yhan0117/gamera_solar/testing/bbr/sensor mount/Sensor mount level 2 v7.step

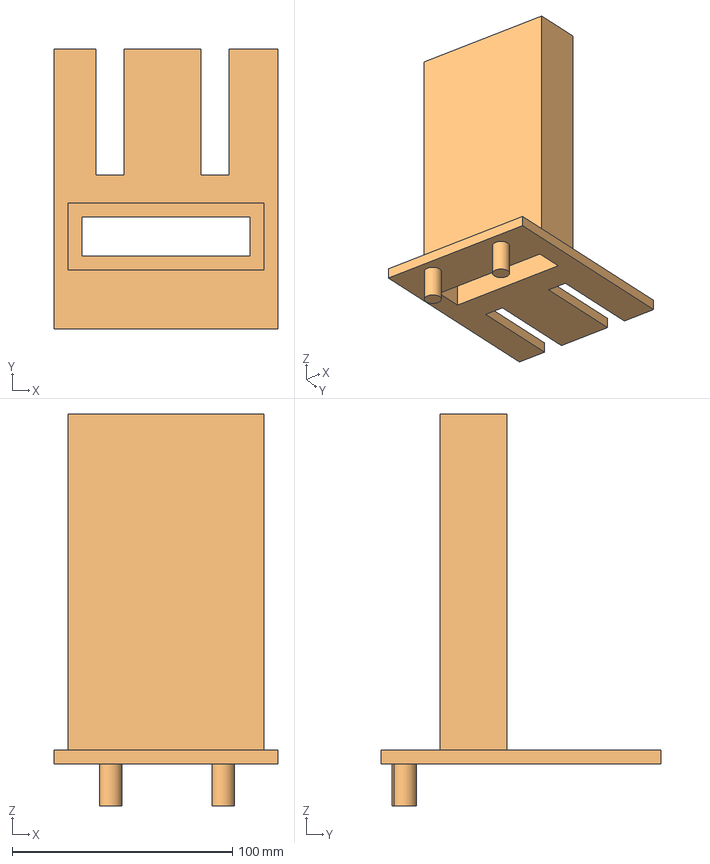
[picture p13: CAD file, 2023-09-21]
testing/bbr/sensor mount/Sensor mount level 2 v7.step
101.6 x 127.0 x 177.8 mm
