yhan0117/gamera_solar/hardware/cad/airframe/arm.SLDPRT

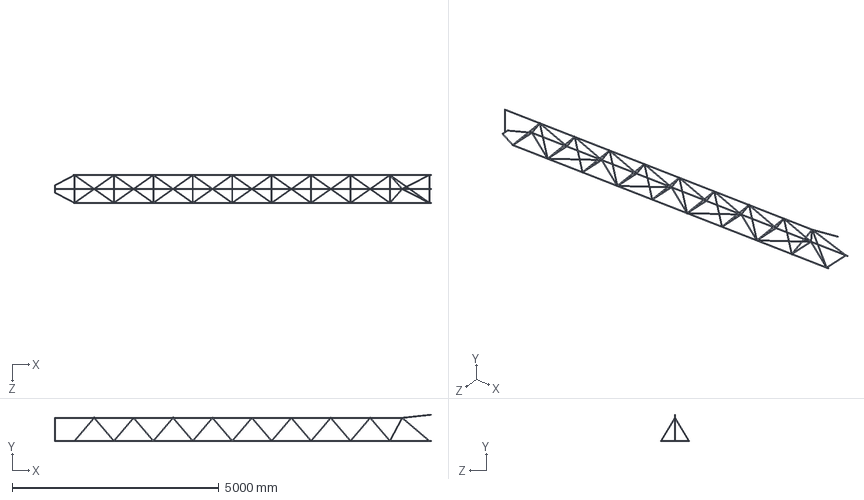
[picture p14: CAD file, 2023-09-18]
hardware/cad/airframe/arm.SLDPRT
9120.2 x 664.4 x 714.2 mm
