yhan0117/gamera_solar/hardware/cad/blades/blade foam/dxf/LESection_2_CCW_Left.dxf

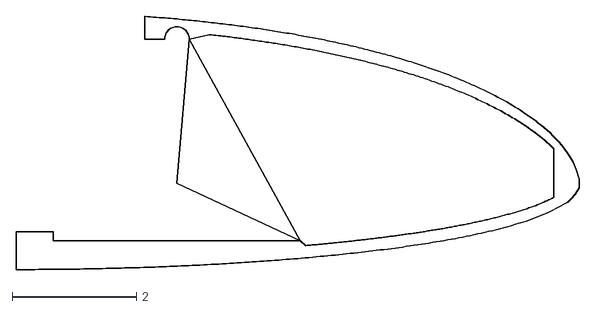
[picture p15: CAD file, 2023-09-21]
hardware/cad/blades/blade foam/dxf/LESection_2_CCW_Left.dxf
9.05 x 4.07
