yhan0117/gamera_solar/hardware/cad/blades/spar core/BladeSparCore.SLDPRT

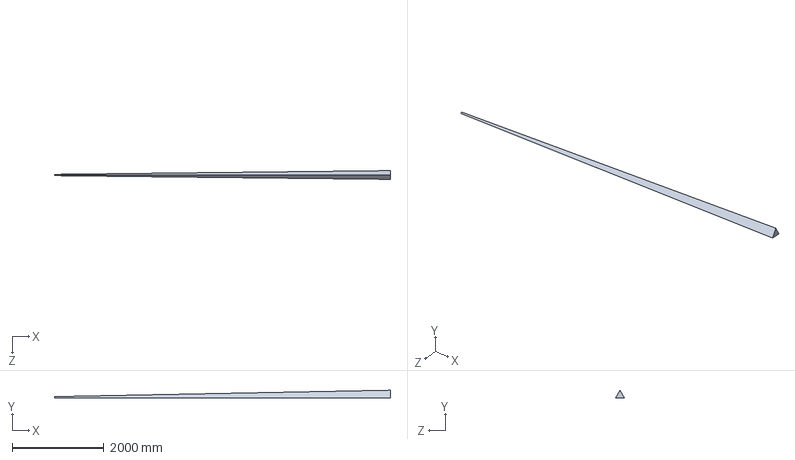
[picture p16: CAD file, 2023-09-21]
hardware/cad/blades/spar core/BladeSparCore.SLDPRT
7315.0 x 165.3 x 190.9 mm
