yhan0117/gamera_solar/hardware/cad/blades/spar core/Core1 (Root)/BladeSparCore1.SLDPRT

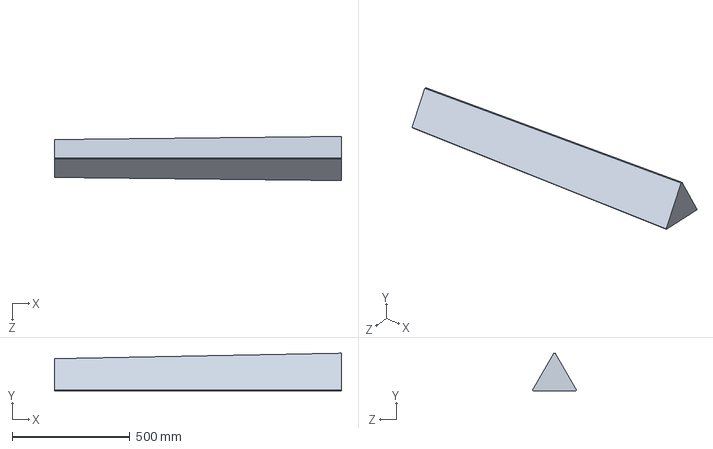
[picture p17: CAD file, 2023-09-21]
hardware/cad/blades/spar core/Core1 (Root)/BladeSparCore1.SLDPRT
1219.0 x 159.8 x 187.7 mm
