yhan0117/gamera_solar/hardware/cad/blades/spar core/Core2/BladeSparCore2.SLDPRT

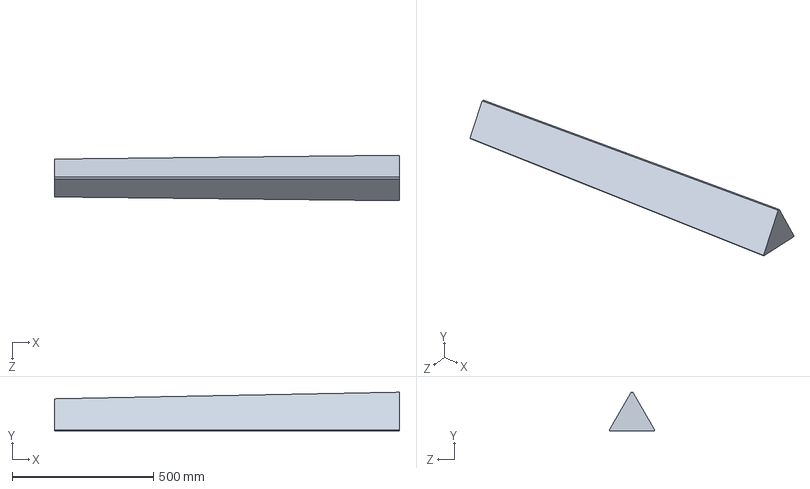
[picture p18: CAD file, 2023-09-21]
hardware/cad/blades/spar core/Core2/BladeSparCore2.SLDPRT
1219.2 x 136.5 x 160.8 mm
