yhan0117/gamera_solar/hardware/cad/blades/spar core/Core4/BladeSparCore4.SLDPRT

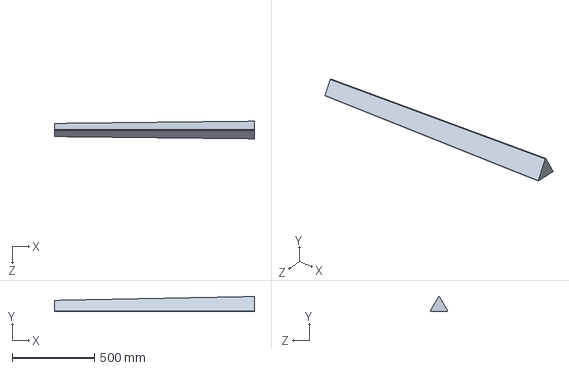
[picture p19: CAD file, 2023-09-21]
hardware/cad/blades/spar core/Core4/BladeSparCore4.SLDPRT
1219.2 x 91.1 x 107.5 mm
