yhan0117/gamera_solar/hardware/cad/blades/spar core/Core6 (Tip)/BladeSparCore6_RightFacepointsplus.DXF

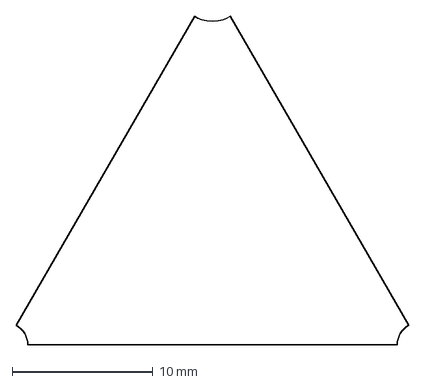
[picture p20: CAD file, 2023-09-21]
hardware/cad/blades/spar core/Core6 (Tip)/BladeSparCore6_RightFacepointsplus.DXF
27.9 x 23.3 mm
