yhan0117/gamera_solar/hardware/cad/rotor/hub/Hub_Pin_A.SLDPRT

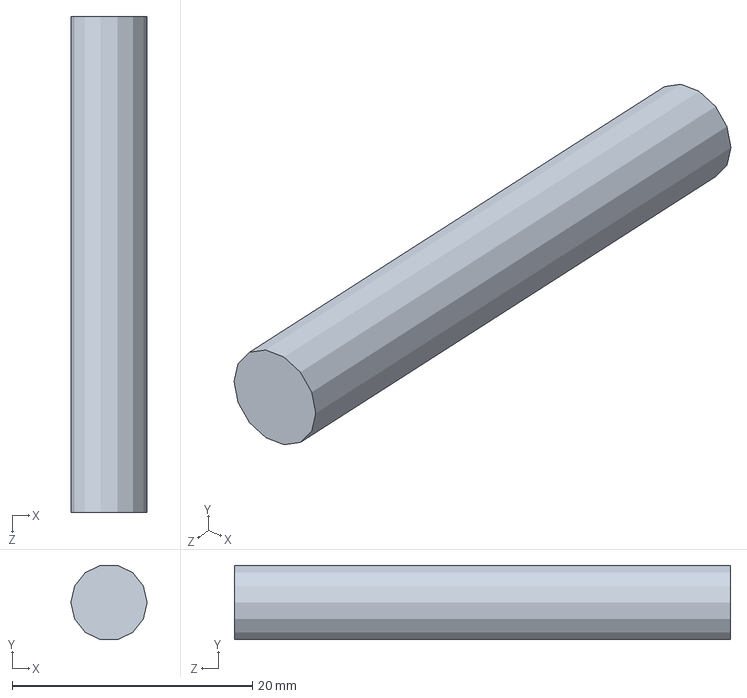
[picture p21: CAD file, 2023-09-21]
hardware/cad/rotor/hub/Hub_Pin_A.SLDPRT
6.35 x 6.19 x 41.3 mm
