yhan0117/gamera_solar/hardware/cad/rotor/landing gear/LG mold B.SLDPRT

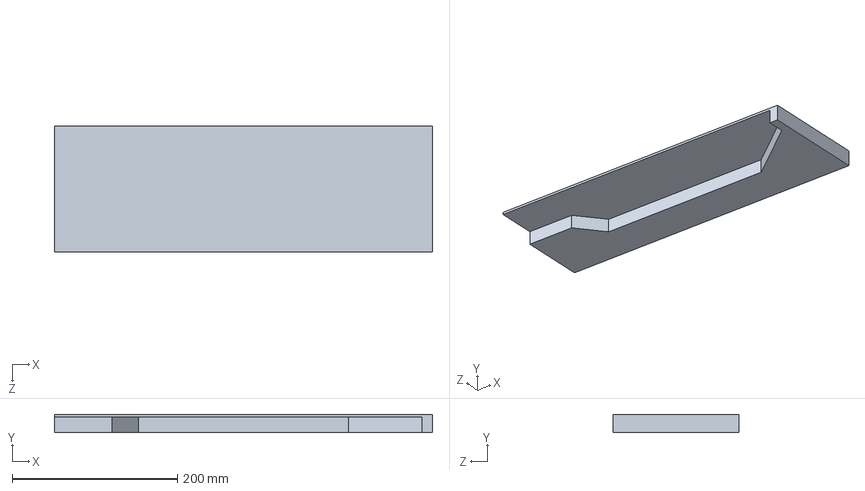
[picture p22: CAD file, 2023-09-21]
hardware/cad/rotor/landing gear/LG mold B.SLDPRT
457.2 x 22.2 x 152.4 mm
