yhan0117/gamera_solar/hardware/cad/rotor/shafts/output_shaft.SLDPRT

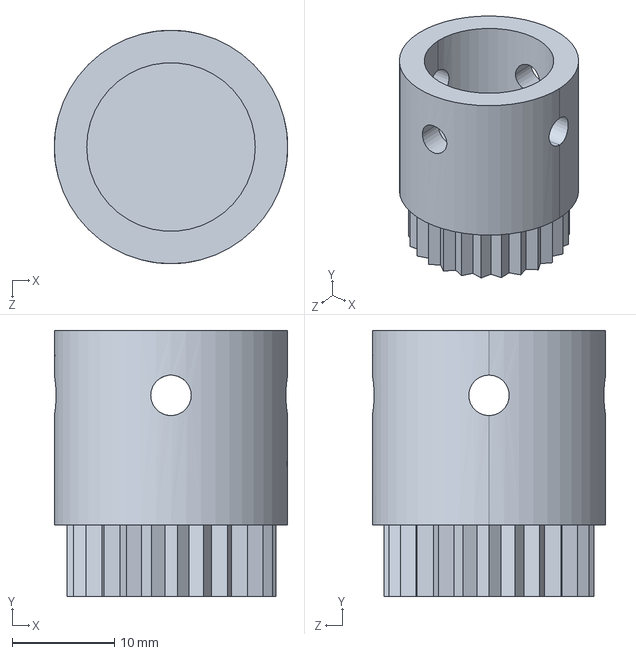
[picture p23: CAD file, 2023-09-21]
hardware/cad/rotor/shafts/output_shaft.SLDPRT
22.9 x 26.1 x 22.9 mm
