yhan0117/gamera_solar/testing/bbr/sensor mount/Sensor Mount base v9.step

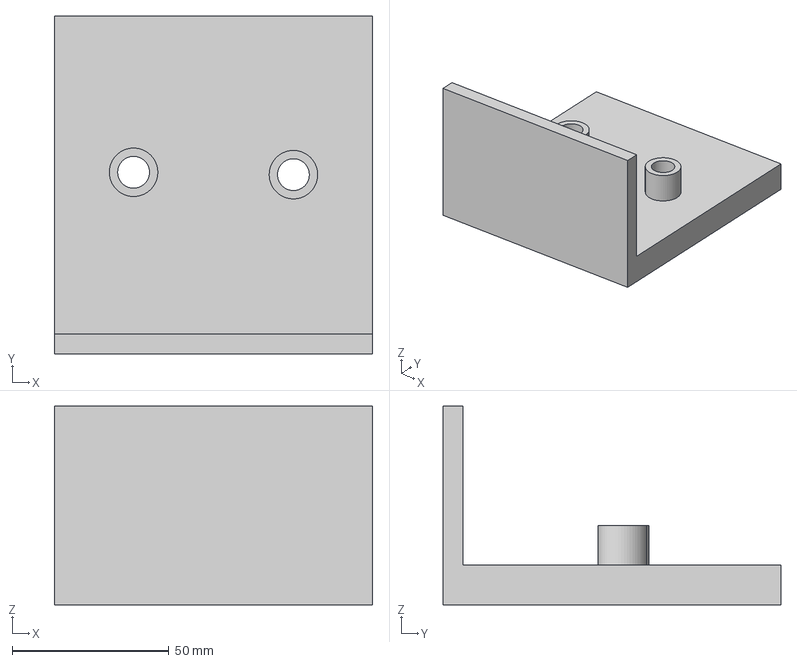
[picture p24: CAD file, 2023-09-21]
testing/bbr/sensor mount/Sensor Mount base v9.step
101.6 x 107.9 x 63.5 mm
