yhan0117/gamera_solar/hardware/cad/airframe/center.SLDPRT

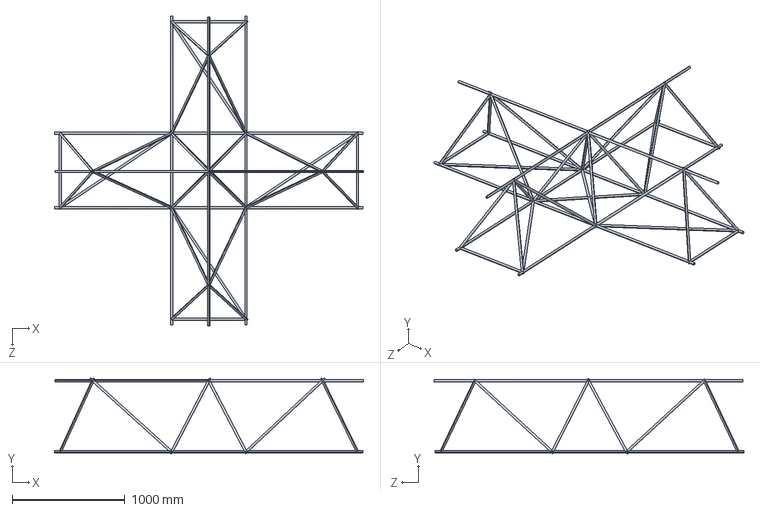
[picture p25: CAD file, 2023-09-18]
hardware/cad/airframe/center.SLDPRT
2745.7 x 673.2 x 2752.9 mm
