yhan0117/gamera_solar/hardware/cad/blades/blade foam/dxf/BladeSection_5_CCW_Right.dxf

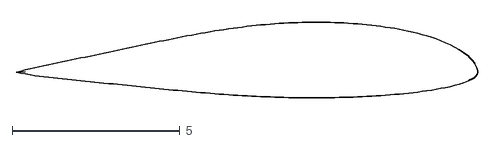
[picture p26: CAD file, 2023-09-21]
hardware/cad/blades/blade foam/dxf/BladeSection_5_CCW_Right.dxf
13.7 x 2.25
