yhan0117/gamera_solar/hardware/cad/blades/spar core/Core1 (Root)/BladeSparCore1B.DXF

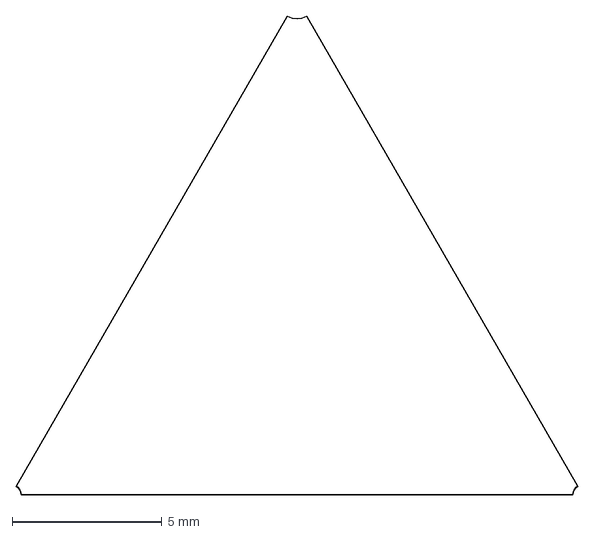
[picture p27: CAD file, 2023-09-21]
hardware/cad/blades/spar core/Core1 (Root)/BladeSparCore1B.DXF
18.8 x 16.0 mm
