yhan0117/gamera_solar/hardware/cad/blades/spar core/Core5/BladeSparCore5_RightFace.DXF

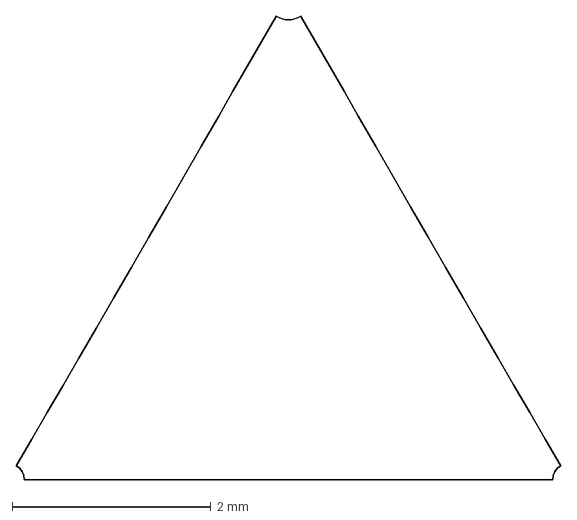
[picture p28: CAD file, 2023-09-21]
hardware/cad/blades/spar core/Core5/BladeSparCore5_RightFace.DXF
5.48 x 4.66 mm
