yhan0117/gamera_solar/hardware/cad/rotor/hub/Hub_Crescent.SLDPRT

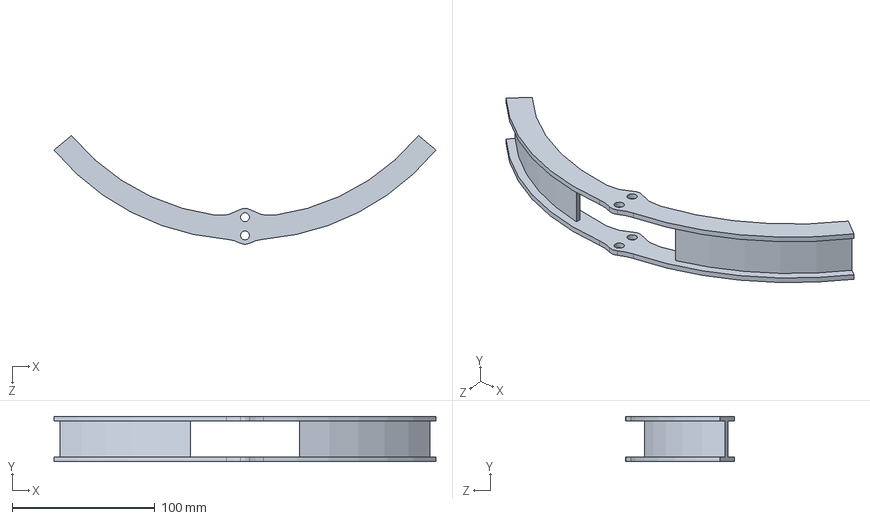
[picture p29: CAD file, 2023-09-21]
hardware/cad/rotor/hub/Hub_Crescent.SLDPRT
267.4 x 31.8 x 76.2 mm
