yhan0117/gamera_solar/hardware/cad/rotor/landing gear/tip_rod.SLDPRT

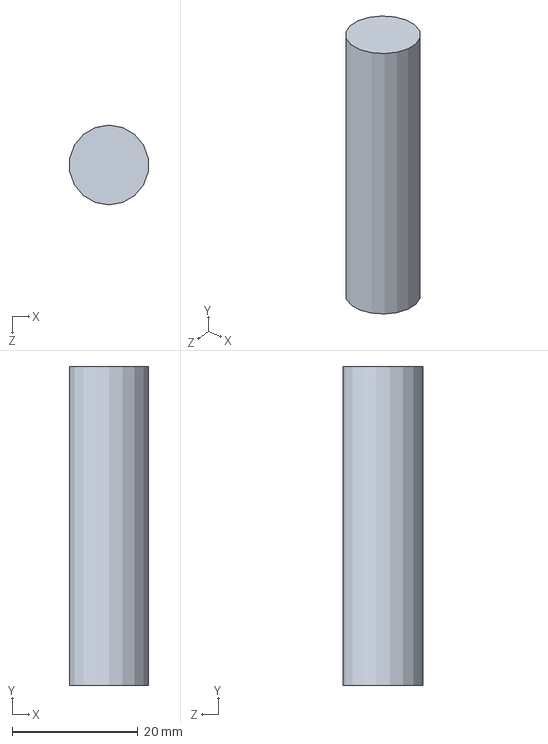
[picture p30: CAD file, 2023-09-21]
hardware/cad/rotor/landing gear/tip_rod.SLDPRT
12.5 x 50.8 x 12.7 mm
