yhan0117/gamera_solar/hardware/cad/rotor/shafts/rotor_shaft.SLDPRT

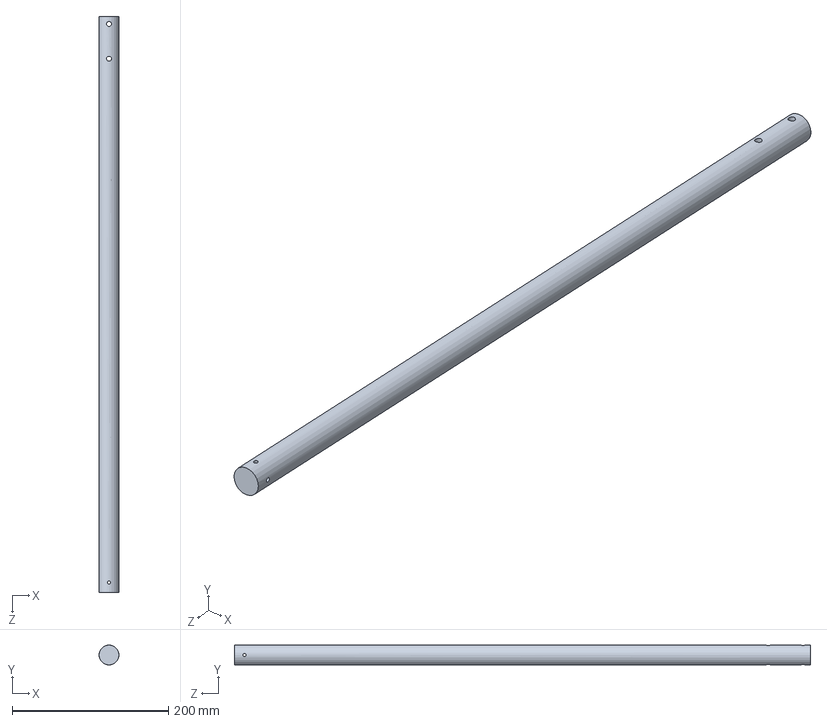
[picture p31: CAD file, 2023-09-21]
hardware/cad/rotor/shafts/rotor_shaft.SLDPRT
25.4 x 25.4 x 736.6 mm
