yhan0117/gamera_solar/testing/bbr/sensor mount/Untitled v2.step

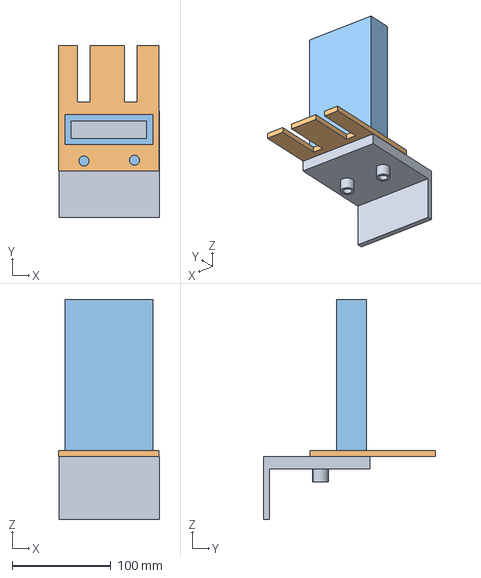
[picture p32: CAD file, 2023-09-21]
testing/bbr/sensor mount/Untitled v2.step
102.1 x 174.1 x 222.3 mm
Sensor Mount base
Sensor mount level 2
