yhan0117/gamera_solar/hardware/cad/blades/blade foam/dxf/LESection_3_CW_Right.dxf

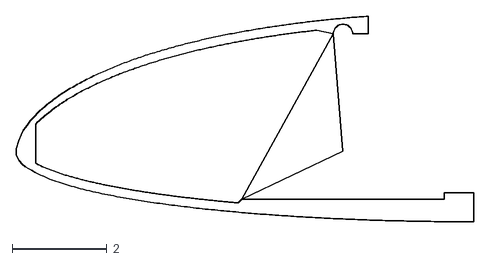
[picture p33: CAD file, 2023-09-21]
hardware/cad/blades/blade foam/dxf/LESection_3_CW_Right.dxf
9.67 x 4.34
