yhan0117/gamera_solar/hardware/cad/blades/spar core/Core1 (Root)/BladeSparCore1A.DXF

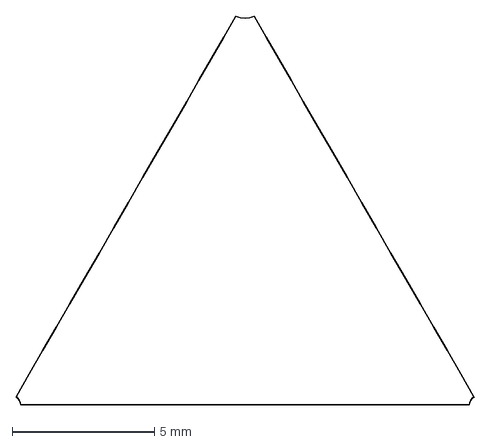
[picture p34: CAD file, 2023-09-21]
hardware/cad/blades/spar core/Core1 (Root)/BladeSparCore1A.DXF
16.1 x 13.7 mm
