yhan0117/gamera_solar/hardware/cad/blades/spar core/Core6 (Tip)/BladeSparCore6_LeftFacepointsplus.DXF

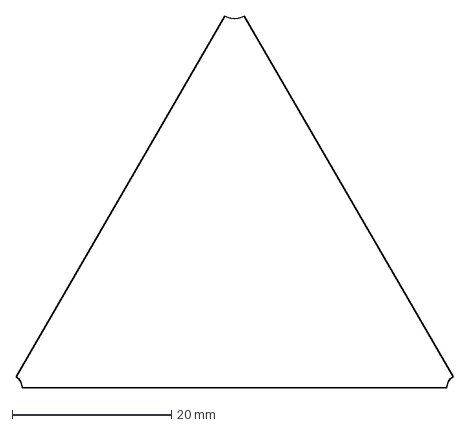
[picture p35: CAD file, 2023-09-21]
hardware/cad/blades/spar core/Core6 (Tip)/BladeSparCore6_LeftFacepointsplus.DXF
54.8 x 46.6 mm
