yhan0117/gamera_solar/hardware/cad/rotor/hub/Hub_block_B.SLDPRT

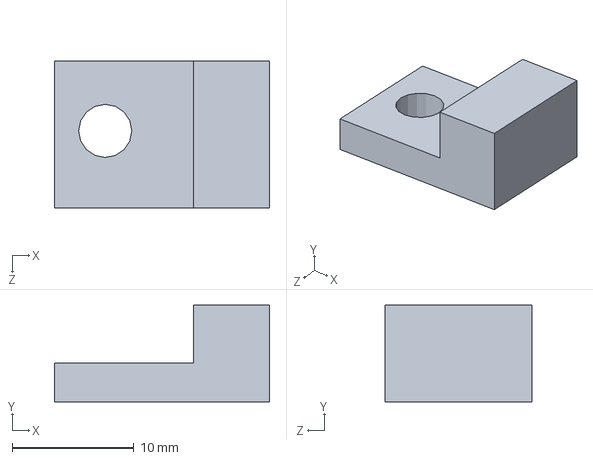
[picture p36: CAD file, 2023-09-21]
hardware/cad/rotor/hub/Hub_block_B.SLDPRT
17.7 x 7.94 x 12.1 mm
