yhan0117/gamera_solar/hardware/cad/rotor/landing gear/LG mold A.SLDPRT

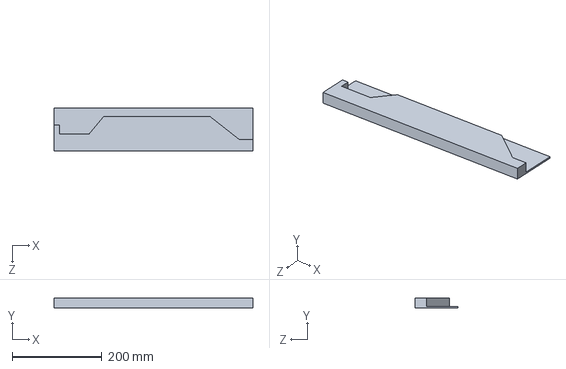
[picture p37: CAD file, 2023-09-21]
hardware/cad/rotor/landing gear/LG mold A.SLDPRT
444.5 x 22.2 x 95.2 mm
