yhan0117/gamera_solar/hardware/cad/blades/blade foam/dxf/BladeSection_4_HollowTE_CW_Right.dxf

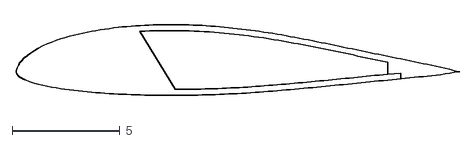
[picture p38: CAD file, 2023-09-21]
hardware/cad/blades/blade foam/dxf/BladeSection_4_HollowTE_CW_Right.dxf
20.6 x 3.29
