yhan0117/gamera_solar/hardware/cad/rotor/hub/Hub_metalspacer.SLDPRT

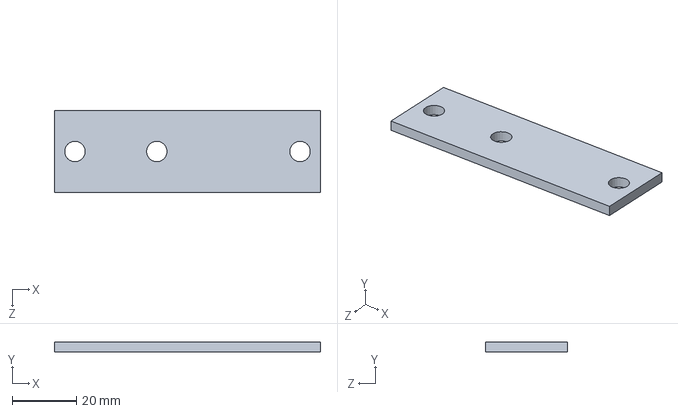
[picture p39: CAD file, 2023-09-21]
hardware/cad/rotor/hub/Hub_metalspacer.SLDPRT
82.5 x 3.17 x 25.4 mm
