yhan0117/gamera_solar/hardware/cad/rotor/shafts/rotor_shaft_bearing.SLDPRT

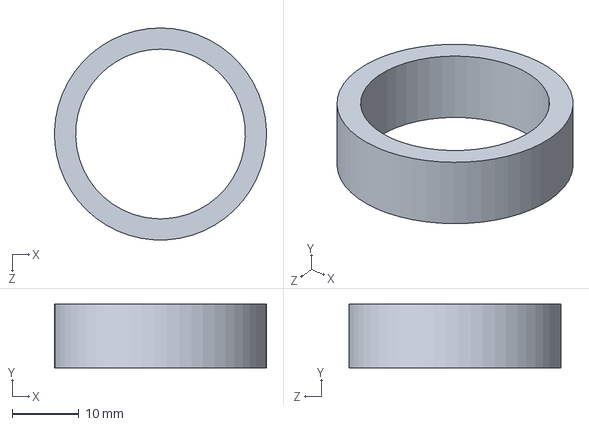
[picture p40: CAD file, 2023-09-21]
hardware/cad/rotor/shafts/rotor_shaft_bearing.SLDPRT
31.7 x 9.53 x 31.8 mm
