yhan0117/gamera_solar/hardware/cad/blades/spar core/Core6 (Tip)/BladeSparCore6.SLDPRT

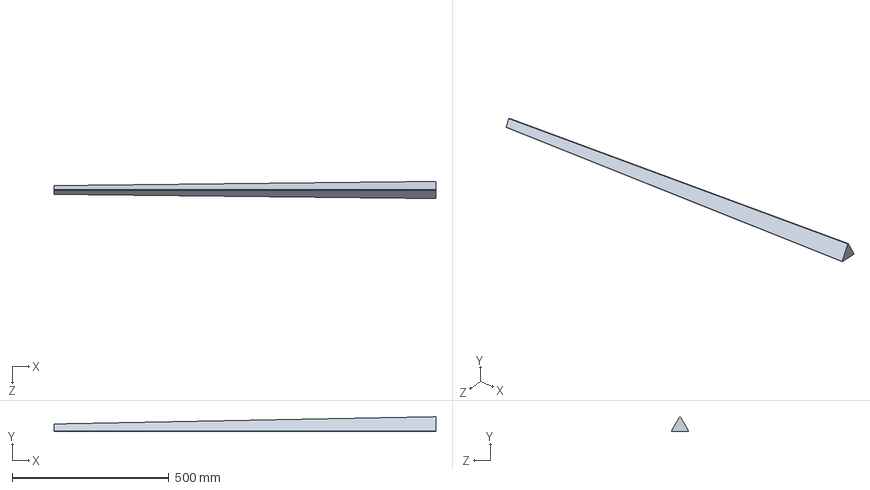
[picture p42: CAD file, 2023-09-21]
hardware/cad/blades/spar core/Core6 (Tip)/BladeSparCore6.SLDPRT
1219.2 x 46.6 x 54.8 mm
