yhan0117/gamera_solar/hardware/cad/rotor/hub/Hub_plasticspacer.SLDPRT

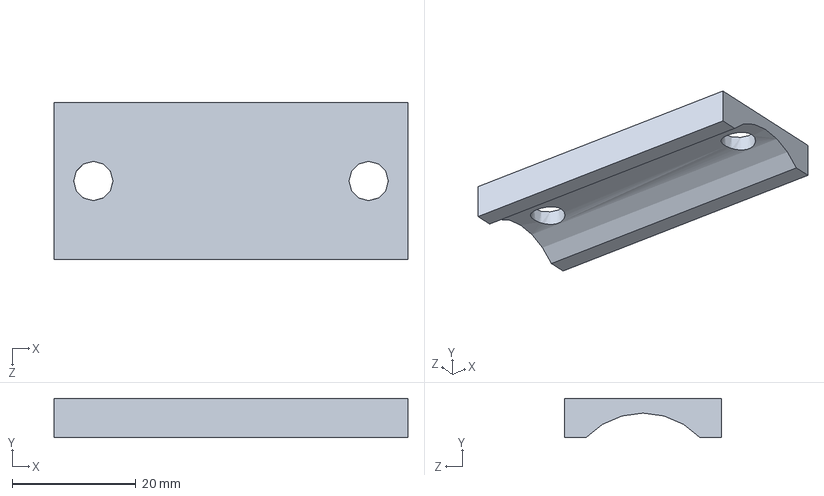
[picture p43: CAD file, 2023-09-21]
hardware/cad/rotor/hub/Hub_plasticspacer.SLDPRT
57.1 x 6.35 x 25.4 mm
