yhan0117/gamera_solar/hardware/cad/rotor/hub/hub_shaft_ccw.SLDPRT

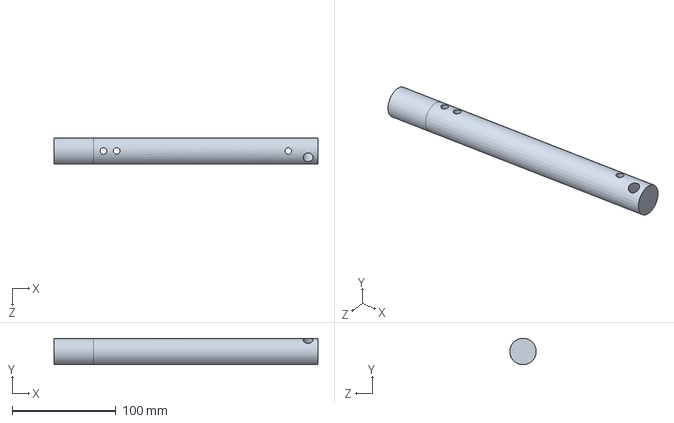
[picture p45: CAD file, 2023-09-21]
hardware/cad/rotor/hub/hub_shaft_ccw.SLDPRT
254.0 x 25.4 x 25.4 mm
