yhan0117/gamera_solar/hardware/cad/blades/blade foam/dxf/LESection_3_CW_Left.dxf

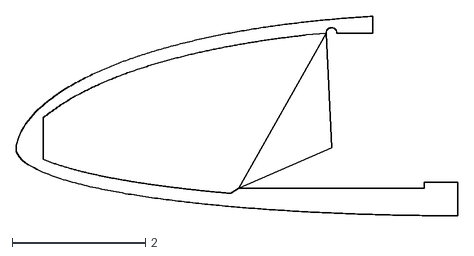
[picture p46: CAD file, 2023-09-21]
hardware/cad/blades/blade foam/dxf/LESection_3_CW_Left.dxf
6.63 x 3.00
