yhan0117/gamera_solar/hardware/cad/blades/blade foam/dxf/LESection_1_CW_Left.dxf

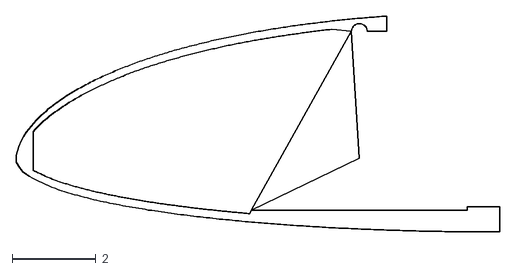
[picture p47: CAD file, 2023-09-21]
hardware/cad/blades/blade foam/dxf/LESection_1_CW_Left.dxf
11.5 x 5.14
