yhan0117/gamera_solar/hardware/cad/blades/blade foam/dxf/LESection_2_CW_Right.dxf

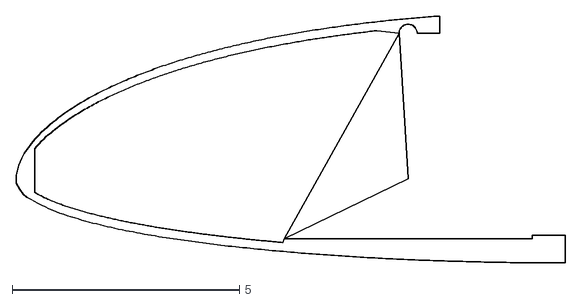
[picture p48: CAD file, 2023-09-21]
hardware/cad/blades/blade foam/dxf/LESection_2_CW_Right.dxf
12.1 x 5.43
