yhan0117/gamera_solar/hardware/cad/blades/blade foam/dxf/BladeSection_4_HollowTE_CCW_Right.dxf

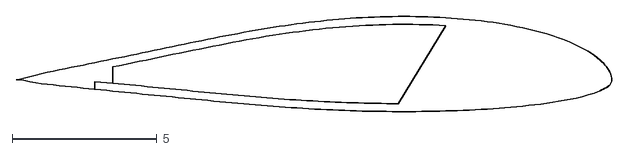
[picture p49: CAD file, 2023-09-21]
hardware/cad/blades/blade foam/dxf/BladeSection_4_HollowTE_CCW_Right.dxf
20.6 x 3.29
