yhan0117/gamera_solar/hardware/cad/blades/blade foam/dxf/BladeSection_5_CW_Left.dxf

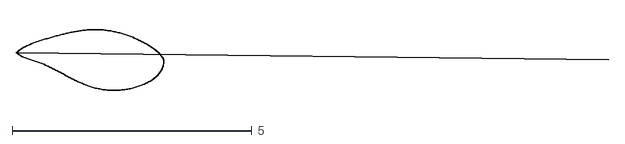
[picture p51: CAD file, 2023-09-21]
hardware/cad/blades/blade foam/dxf/BladeSection_5_CW_Left.dxf
12.3 x 1.27
