yhan0117/gamera_solar/hardware/cad/blades/blade foam/dxf/LESection1_CCW_Left.dxf

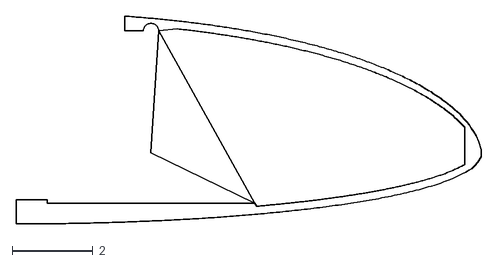
[picture p52: CAD file, 2023-09-21]
hardware/cad/blades/blade foam/dxf/LESection1_CCW_Left.dxf
11.5 x 5.14
