yhan0117/gamera_solar/hardware/cad/blades/blade foam/dxf/LESection_3_CCW_Right.dxf

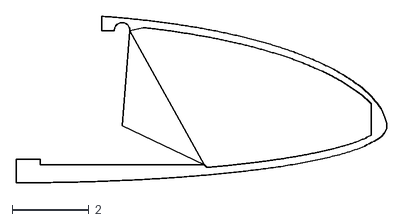
[picture p53: CAD file, 2023-09-21]
hardware/cad/blades/blade foam/dxf/LESection_3_CCW_Right.dxf
9.67 x 4.34
