yhan0117/gamera_solar/hardware/cad/blades/blade foam/dxf/LESection_1_CW_Right.dxf

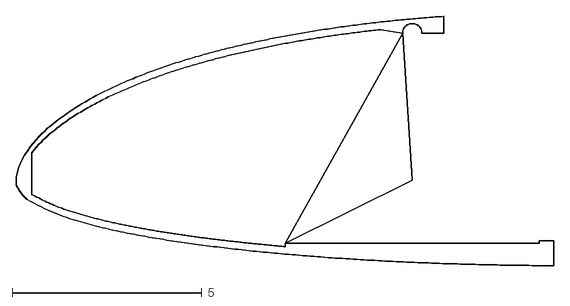
[picture p55: CAD file, 2023-09-21]
hardware/cad/blades/blade foam/dxf/LESection_1_CW_Right.dxf
14.2 x 6.57
